hackersanddesigners/not_makey/images/lib_movingavg.png

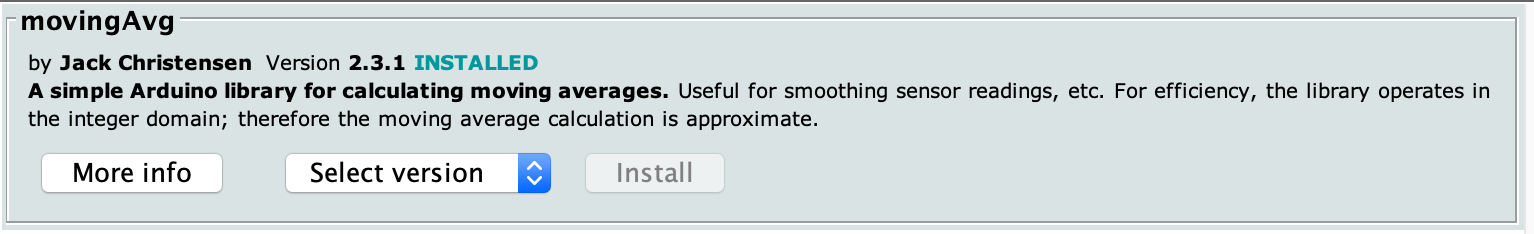
images/lib_movingavg.png
