hackersanddesigners/not_makey/images/simple_boardlayout_bottom.png

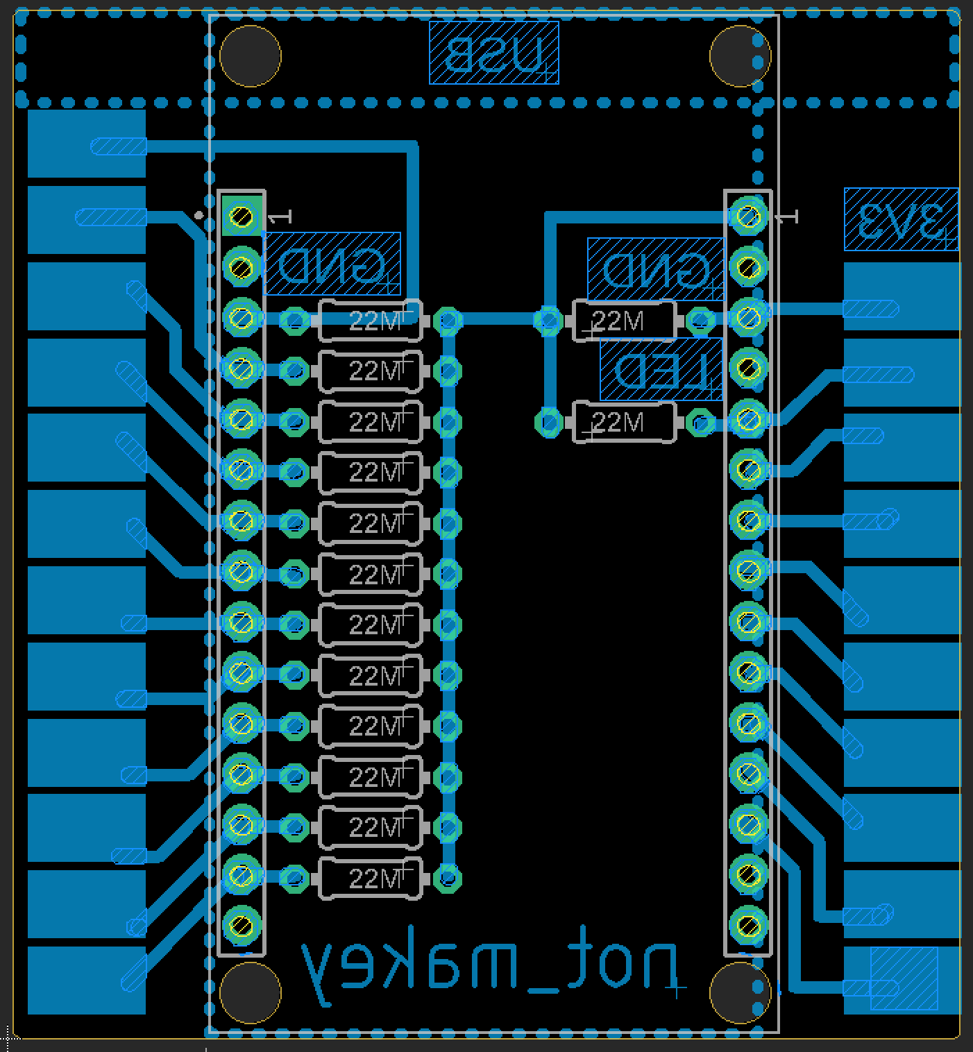
images/simple_boardlayout_bottom.png
