hackersanddesigners/not_makey/fabrication/v1/bottom_v1.png

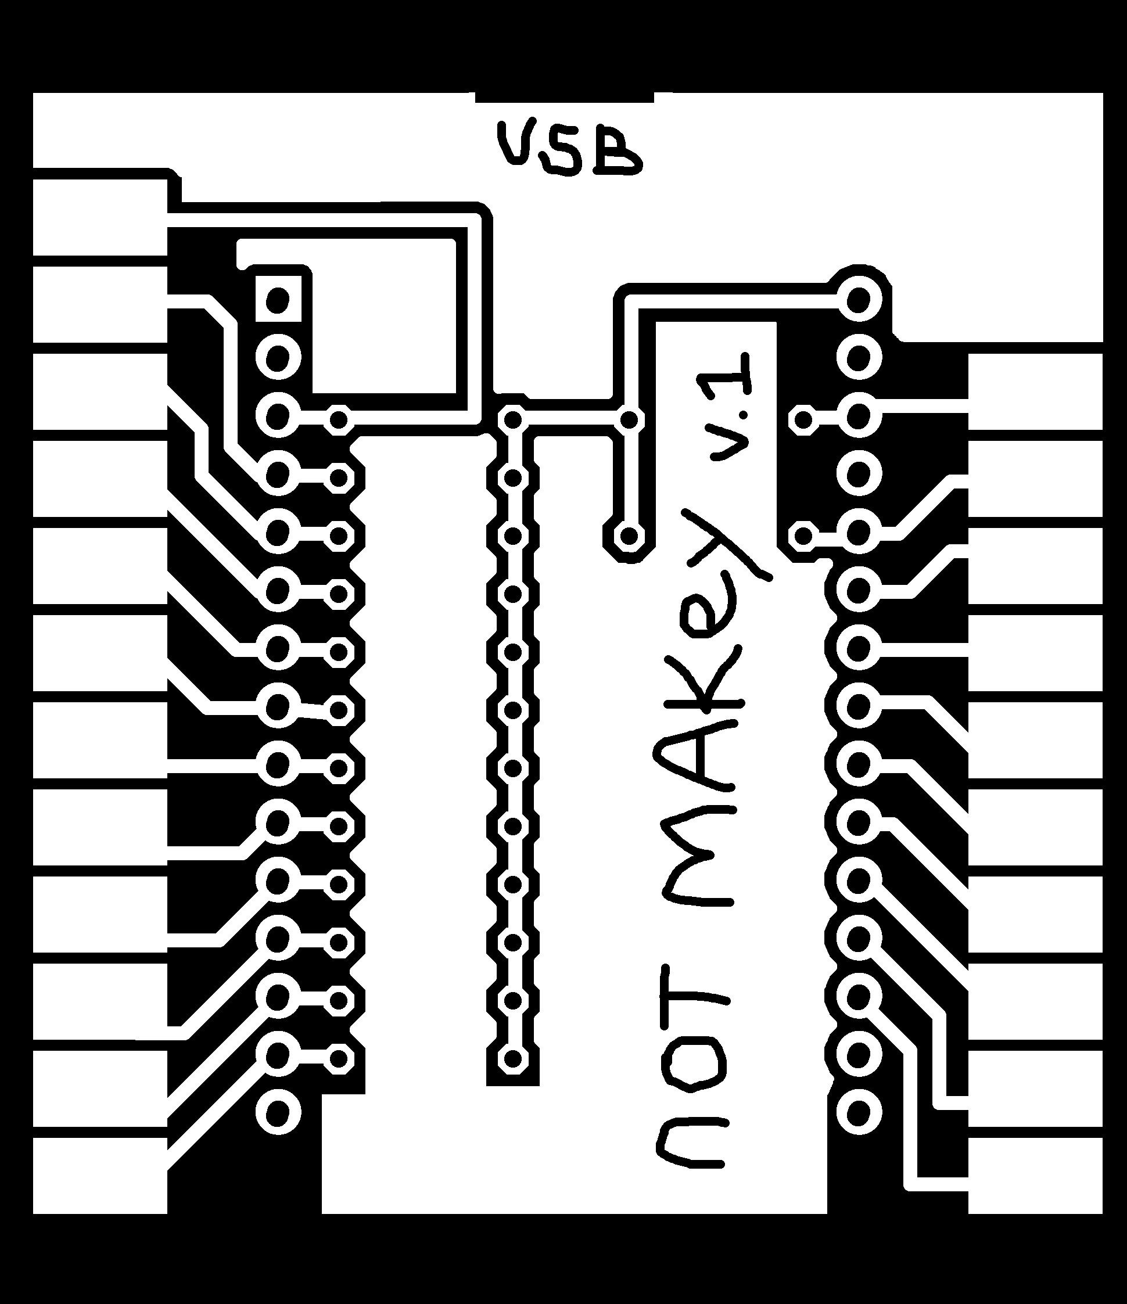
fabrication/v1/bottom_v1.png
