hackersanddesigners/not_makey/fabrication/v1/dimension_v1.png

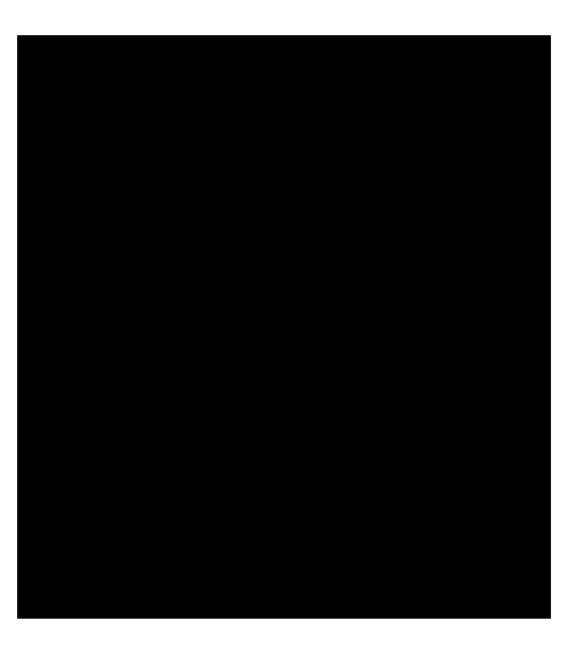
fabrication/v1/dimension_v1.png
