hackersanddesigners/not_makey/fabrication/v1/holes_v1.png

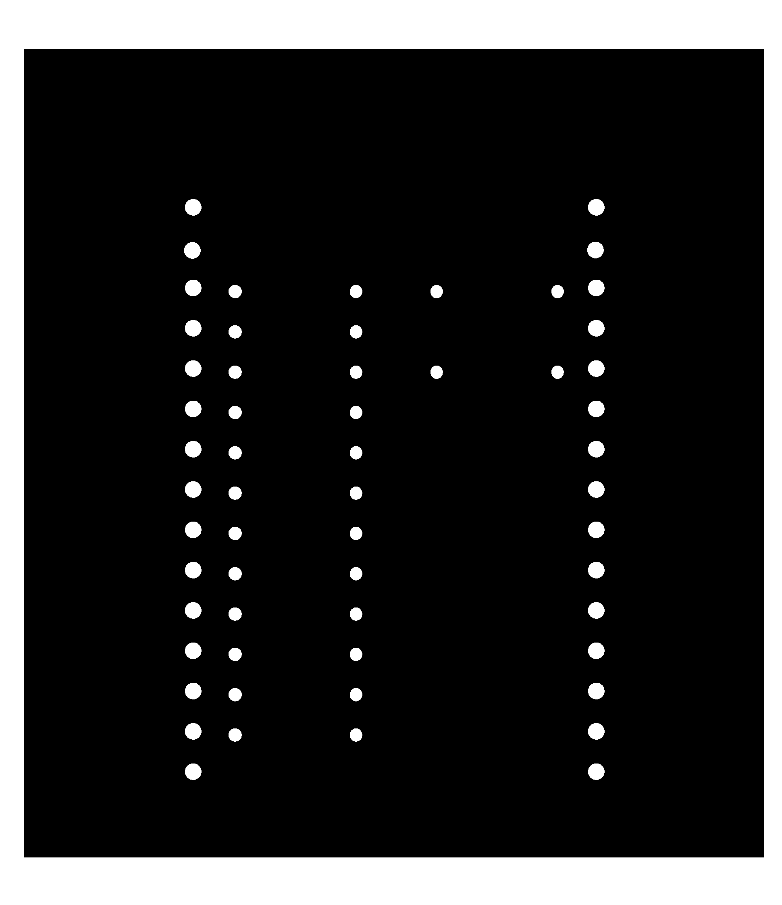
fabrication/v1/holes_v1.png
