hackersanddesigners/not_makey/images/soldered_bot.jpeg

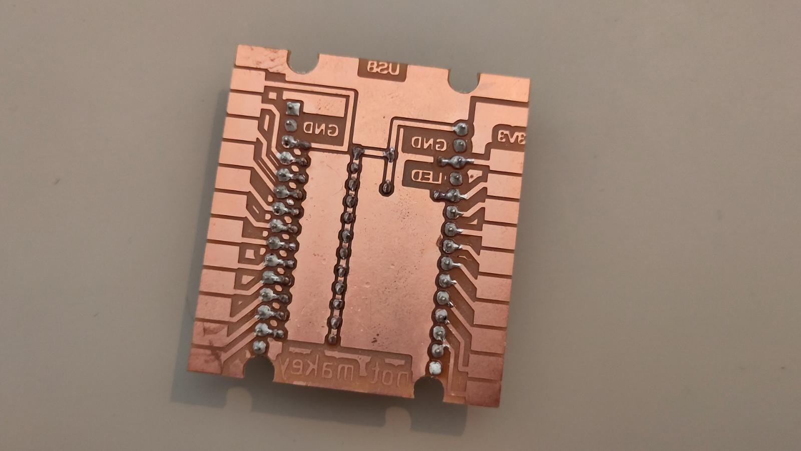
images/soldered_bot.jpeg
