hackersanddesigners/not_makey/images/soldered_top.jpeg

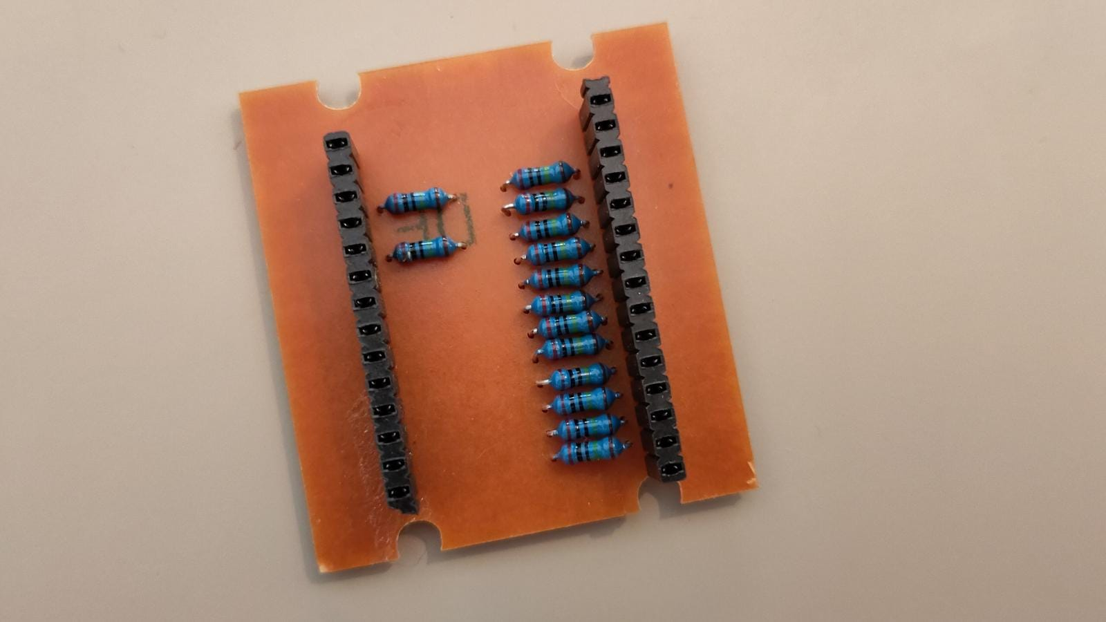
images/soldered_top.jpeg
